schuhumi/autocut/Electronics/Mowing Module/plot/maehwerktreiber-B_Cu.png

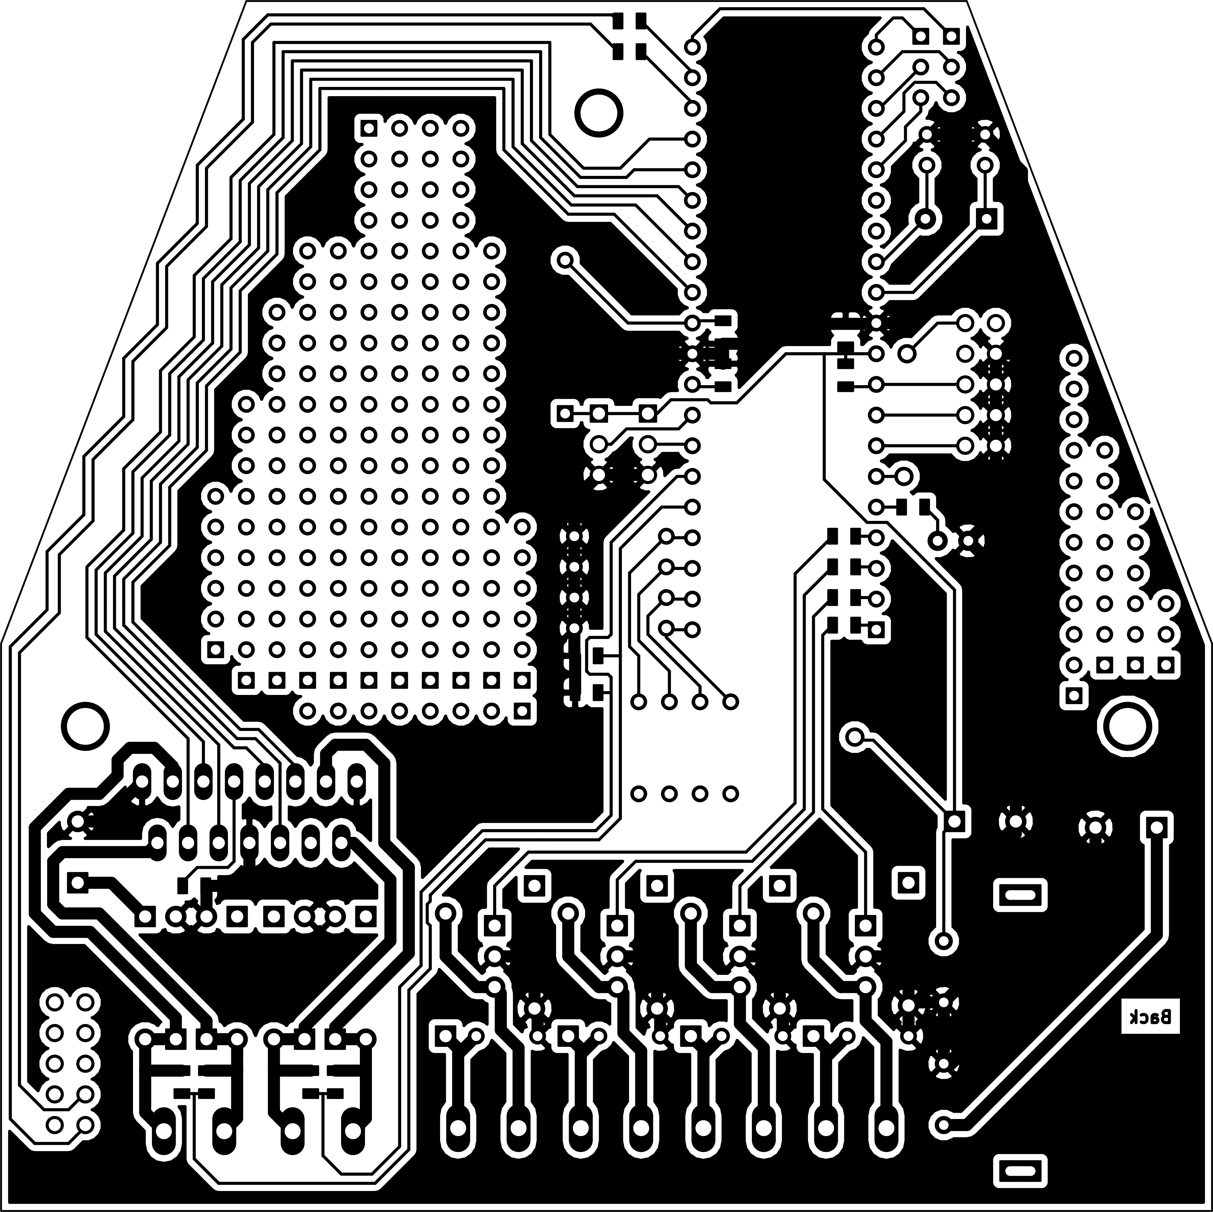
Electronics/Mowing Module/plot/maehwerktreiber-B_Cu.png
