schuhumi/autocut/Electronics/Mowing Module/plot/maehwerktreiber-F_Cu.png

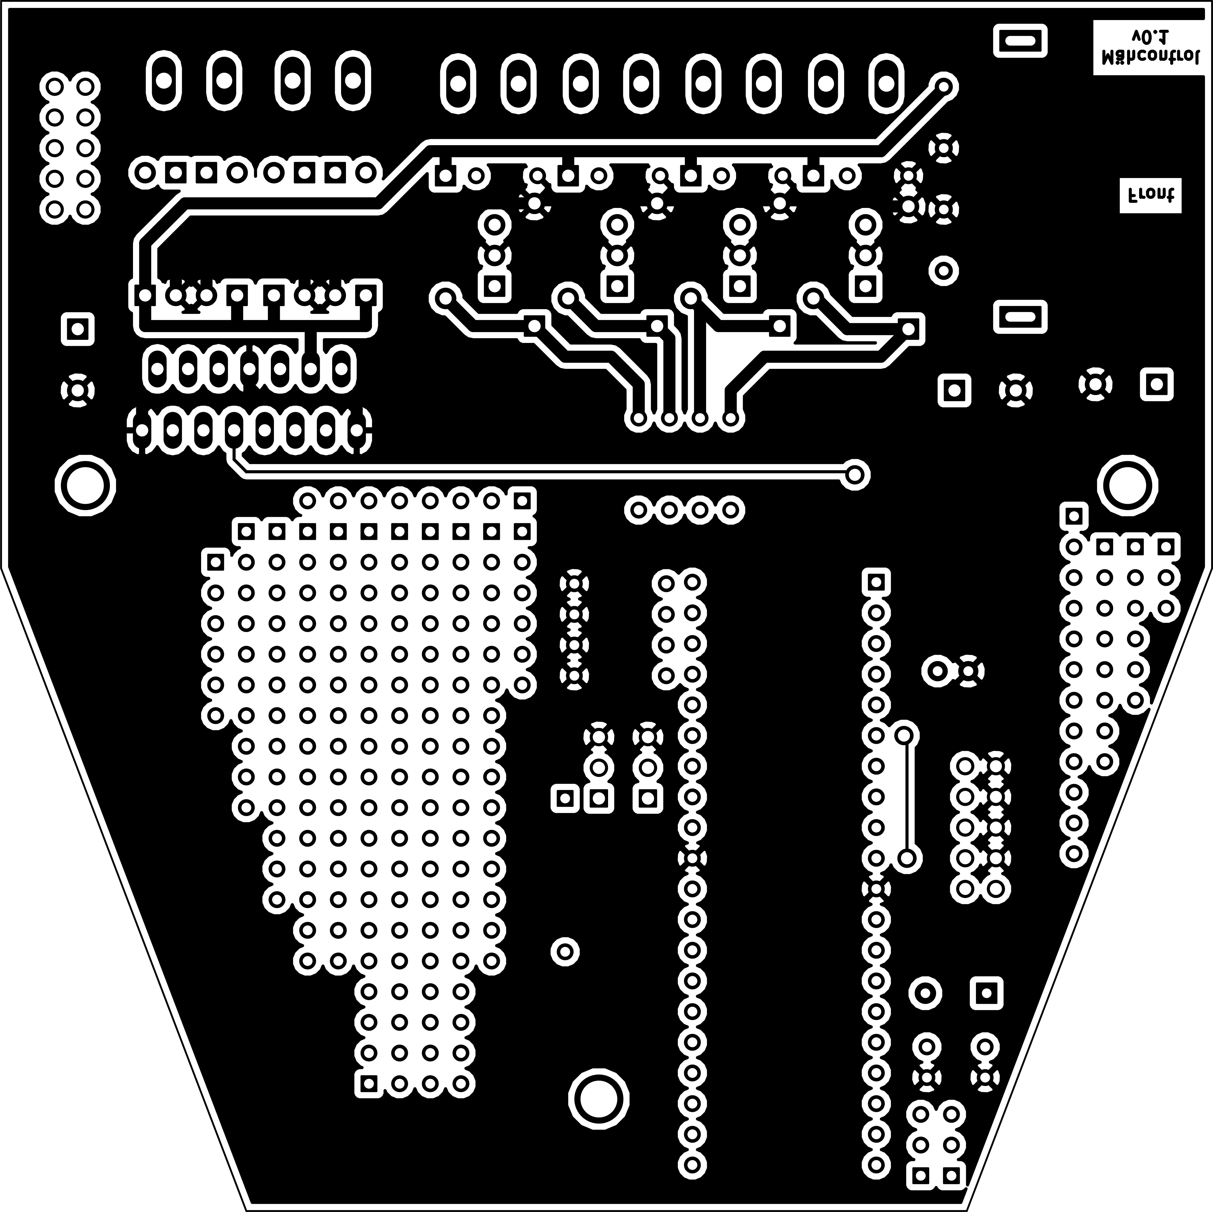
Electronics/Mowing Module/plot/maehwerktreiber-F_Cu.png
