schuhumi/autocut/Sketchboard/Overview - Environment/Overview - Environment.png

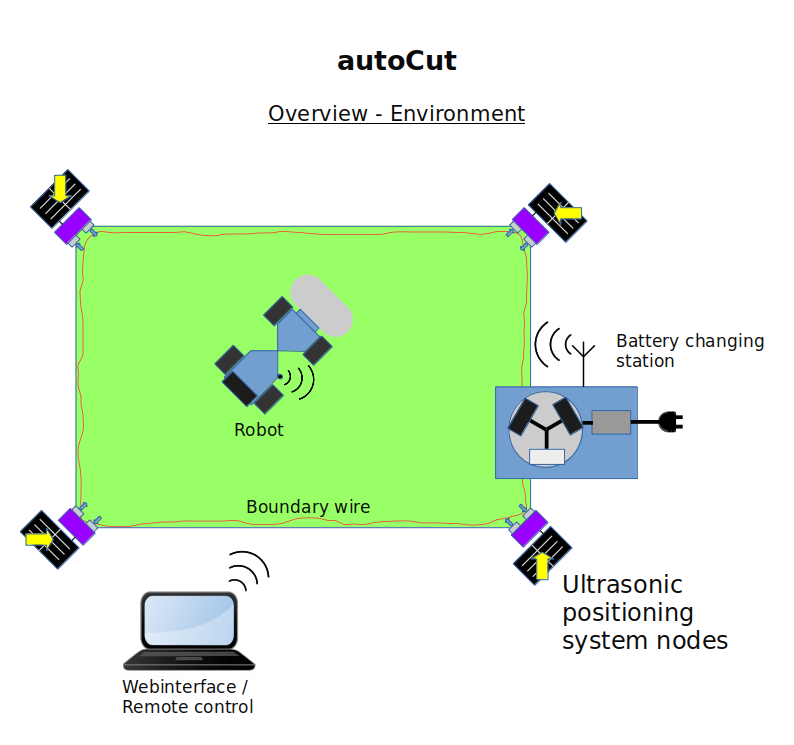
Sketchboard/Overview - Environment/Overview - Environment.png
