schuhumi/autocut/Sketchboard/Ultrasonic Positioning System/Positioning-System.png

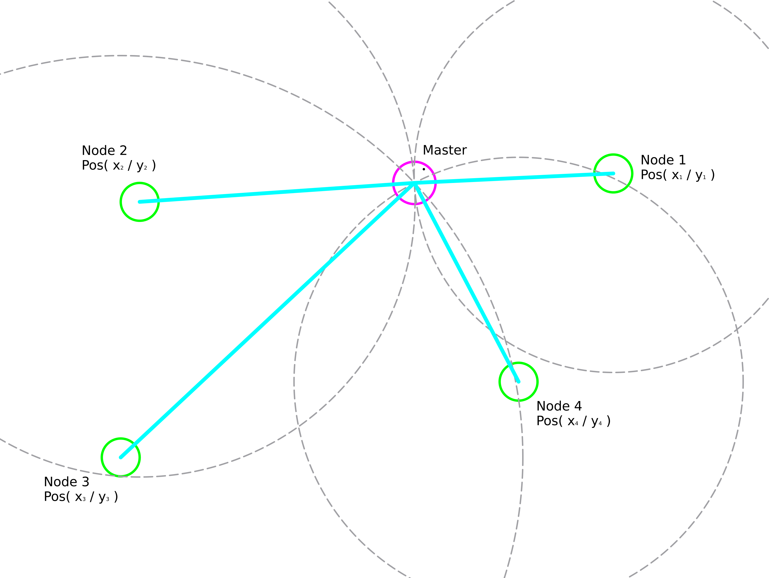
Sketchboard/Ultrasonic Positioning System/Positioning-System.png
